Demetrius-Ross/SimMonitor/images/image.png

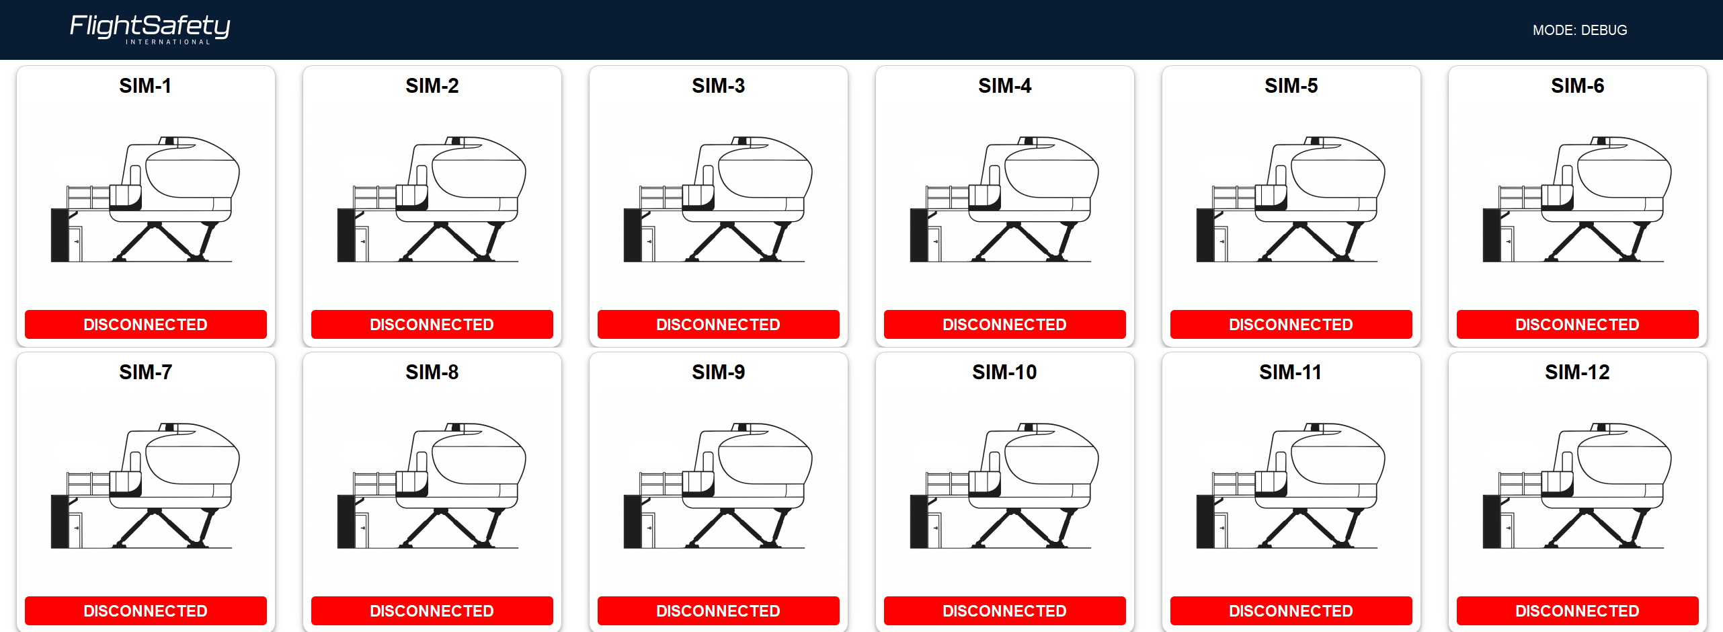
images/image.png
