Demetrius-Ross/SimMonitor/sim_monitor/BACKUP-V1.1/images/FINAL-RAMP-UP.png

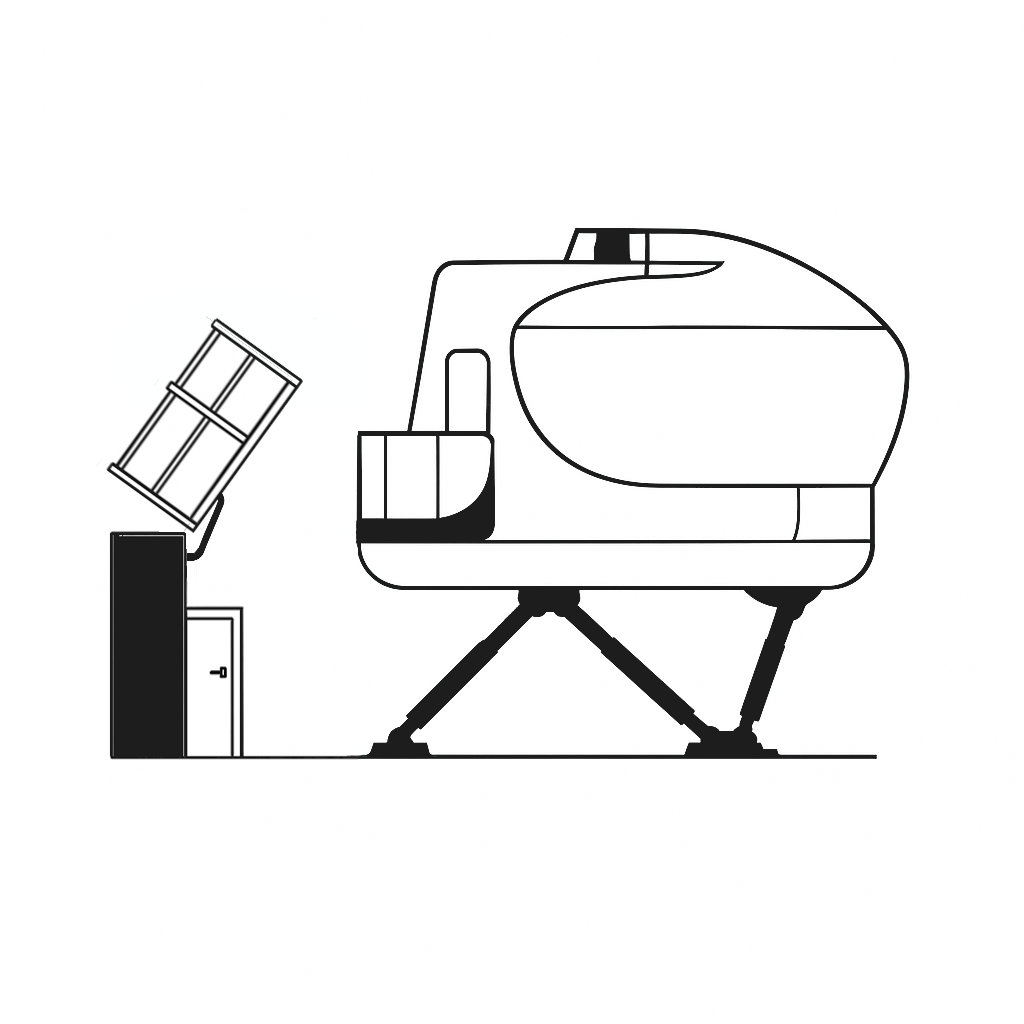
sim_monitor/BACKUP-V1.1/images/FINAL-RAMP-UP.png
