Demetrius-Ross/SimMonitor/sim_monitor/BACKUP-V1.1/images/FINAL-SIM-UP-NO-RAMP.png

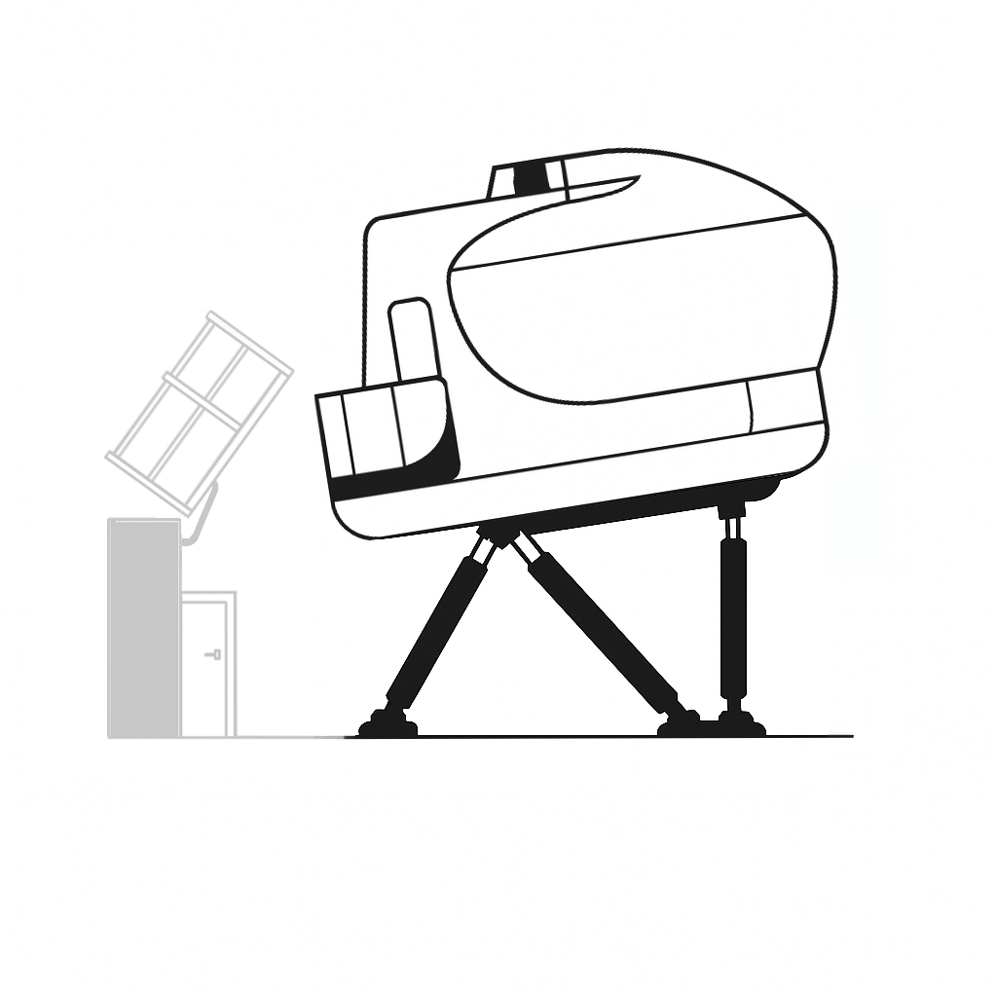
sim_monitor/BACKUP-V1.1/images/FINAL-SIM-UP-NO-RAMP.png
