Demetrius-Ross/SimMonitor/sim_monitor/NEW/images/FINAL-RAMP-UP-ICE.png

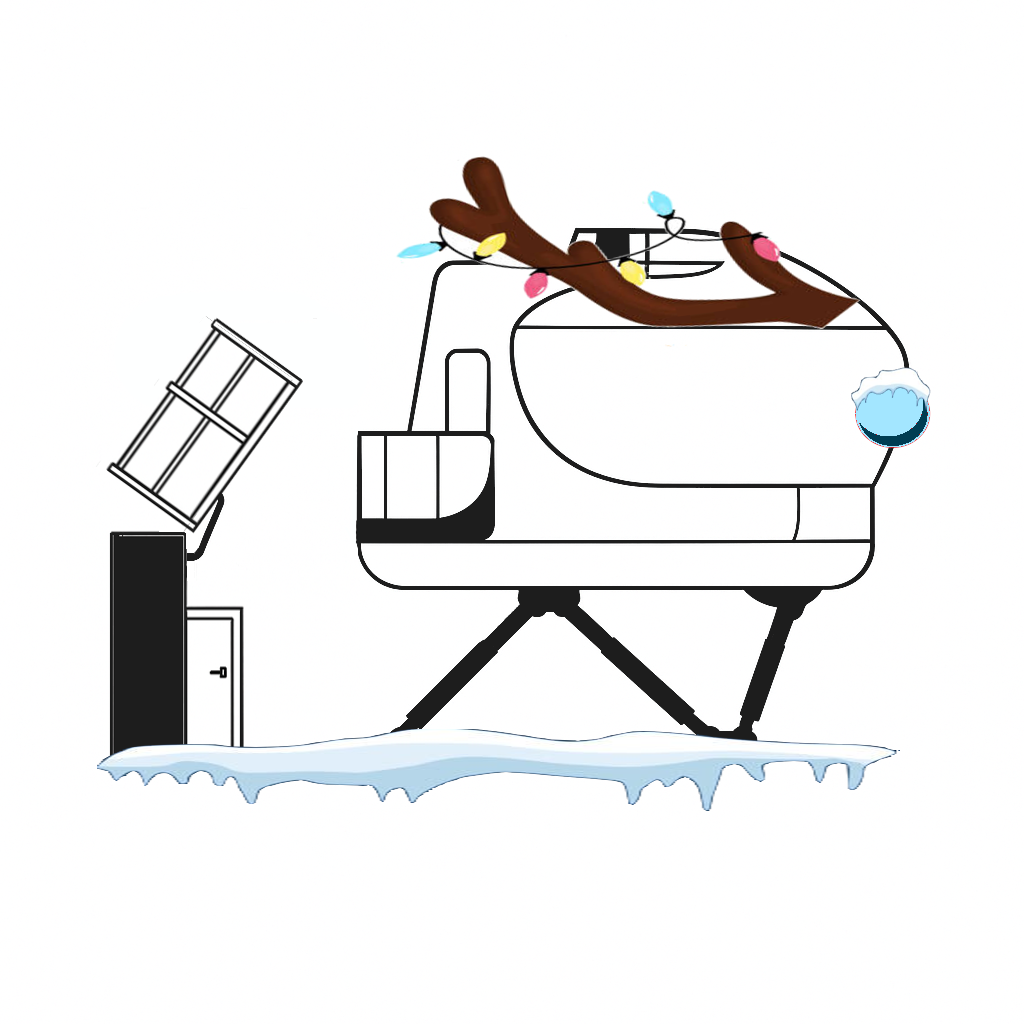
sim_monitor/NEW/images/FINAL-RAMP-UP-ICE.png
