Demetrius-Ross/SimMonitor/sim_monitor/NEW/images/FINAL-SIM-UP-ICE.png

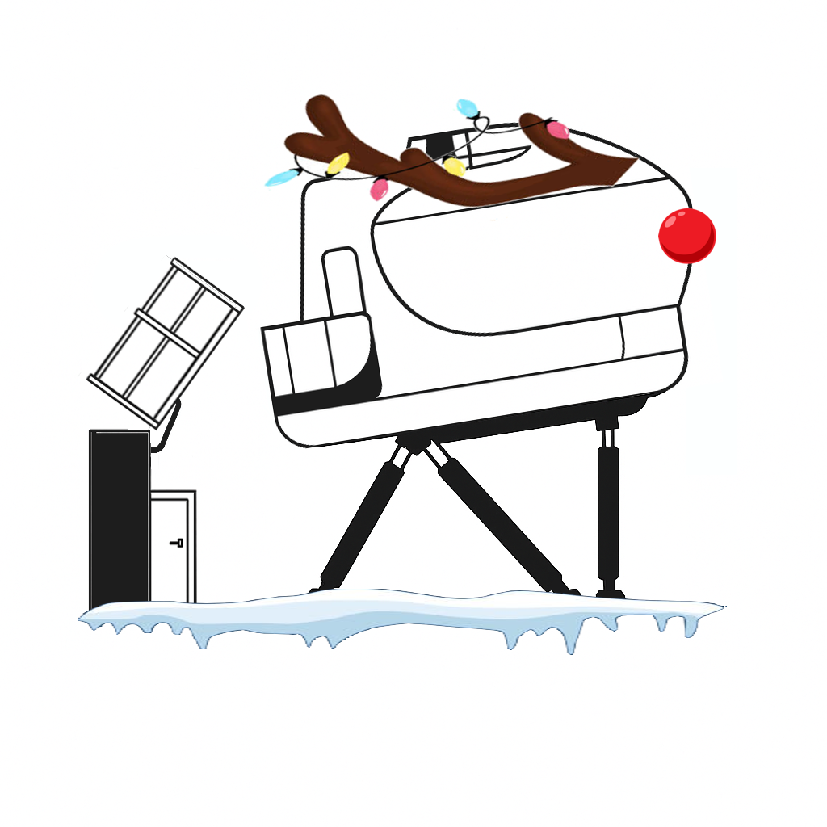
sim_monitor/NEW/images/FINAL-SIM-UP-ICE.png
