Demetrius-Ross/SimMonitor/Hardware-Design/board_MKIV/models/model/COM-16347_SPK.step

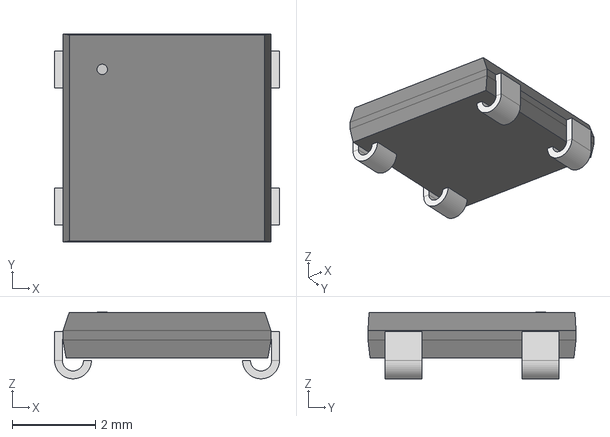
[picture p23: CAD file, 2025-11-21]
Hardware-Design/board_MKIV/models/model/COM-16347_SPK.step
5.41 x 5.00 x 1.60 mm
