Demetrius-Ross/SimMonitor/Hardware-Design/board_telemetry/board_telemetry/models/model/DS01C-254-S-03BE.step

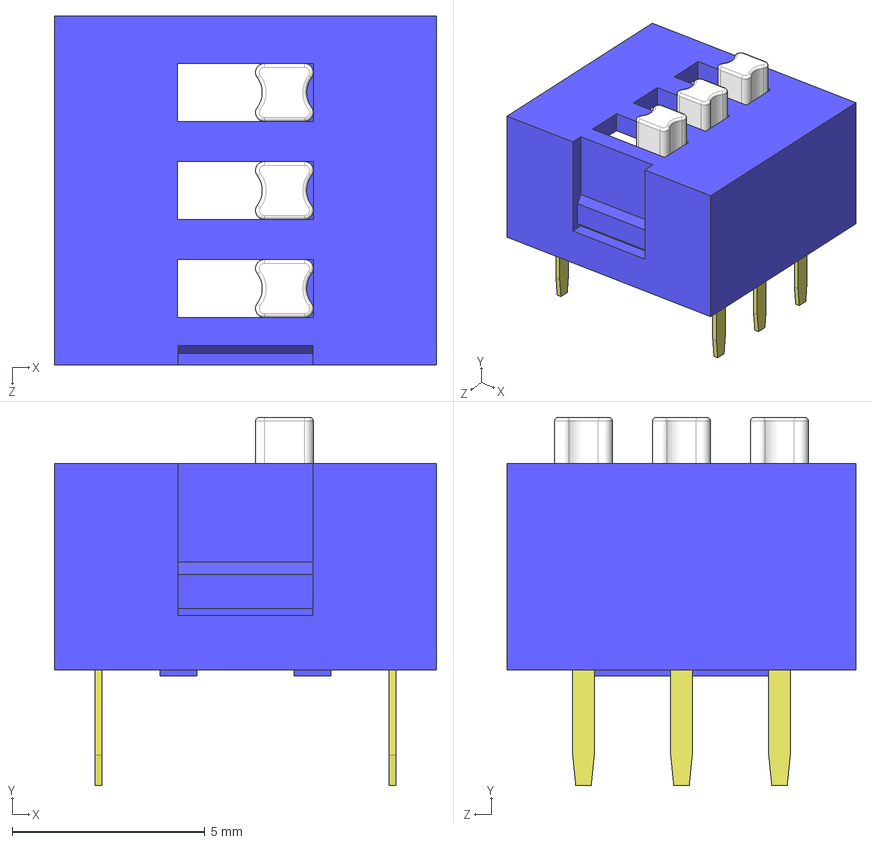
[picture p24: CAD file, 2025-11-19]
Hardware-Design/board_telemetry/board_telemetry/models/model/DS01C-254-S-03BE.step
9.90 x 9.55 x 9.04 mm
