Demetrius-Ross/SimMonitor/Hardware-Design/board_telemetry/board_telemetry/models/model/PB400EEQR1BLK.step

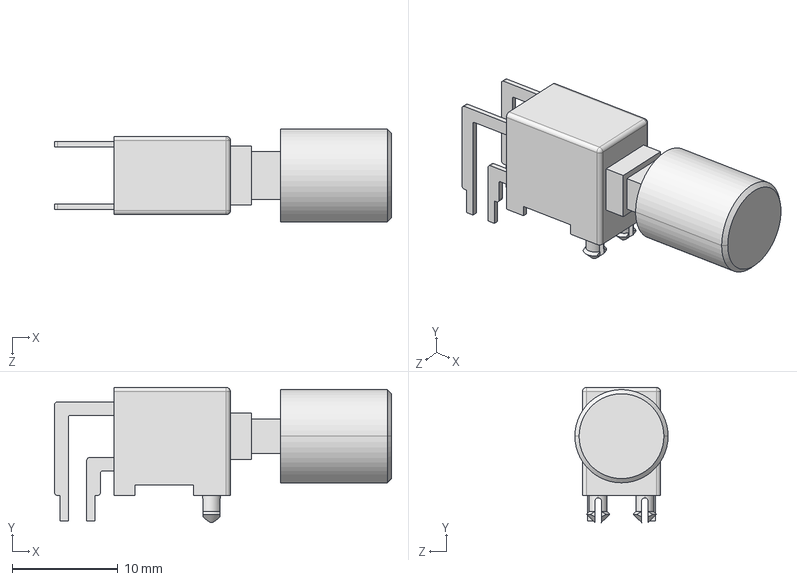
[picture p25: CAD file, 2025-11-15]
Hardware-Design/board_telemetry/board_telemetry/models/model/PB400EEQR1BLK.step
31.8 x 12.7 x 8.80 mm
