Demetrius-Ross/SimMonitor/Hardware-Design/board_telemetry/board_telemetry/models/model/SH-7070TB_7P1X7P3_NDC.step

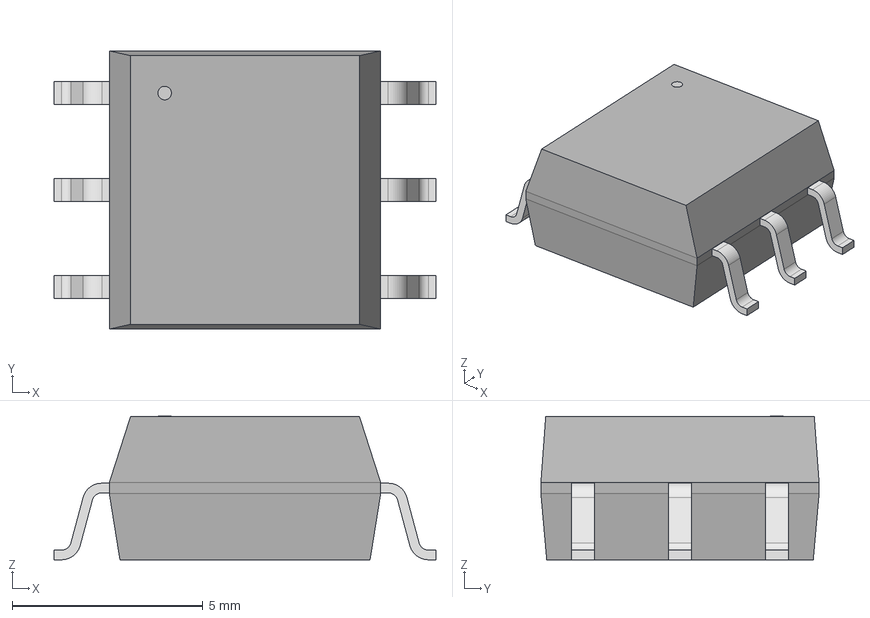
[picture p26: CAD file, 2025-11-15]
Hardware-Design/board_telemetry/board_telemetry/models/model/SH-7070TB_7P1X7P3_NDC.step
10.0 x 7.29 x 3.76 mm
