Demetrius-Ross/SimMonitor/Hardware/board_design/models/model/TO252-3_ROM.step

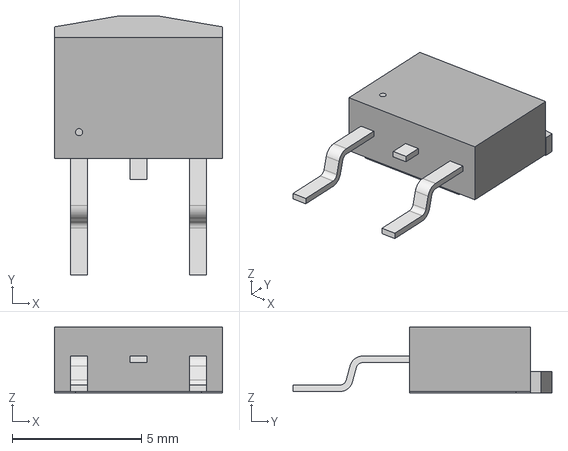
[picture p27: CAD file, 2025-11-06]
Hardware/board_design/models/model/TO252-3_ROM.step
6.50 x 10.0 x 2.54 mm
