Demetrius-Ross/SimMonitor/Hardware-Design/board_telemetry/board_telemetry/models/model/20_pin_straight.STEP

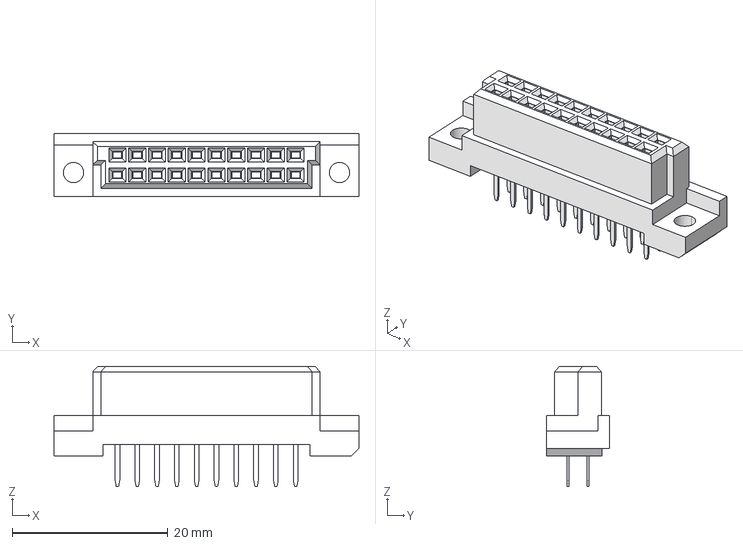
[picture p28: CAD file, 2025-11-13]
Hardware-Design/board_telemetry/board_telemetry/models/model/20_pin_straight.STEP
39.1 x 8.10 x 15.4 mm
