Demetrius-Ross/SimMonitor/Hardware-Design/AllModels/20_pin_90.STEP

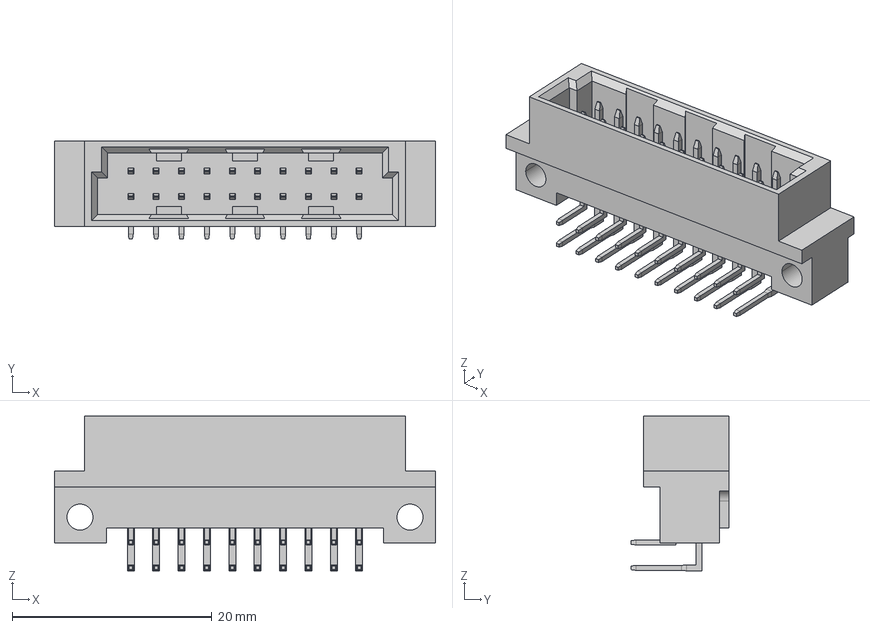
[picture p29: CAD file, 2025-11-13]
Hardware-Design/AllModels/20_pin_90.STEP
38.1 x 9.85 x 15.5 mm
