Demetrius-Ross/SimMonitor/Hardware-Design/board_telemetry/board_telemetry/models/model/D0008A.stp

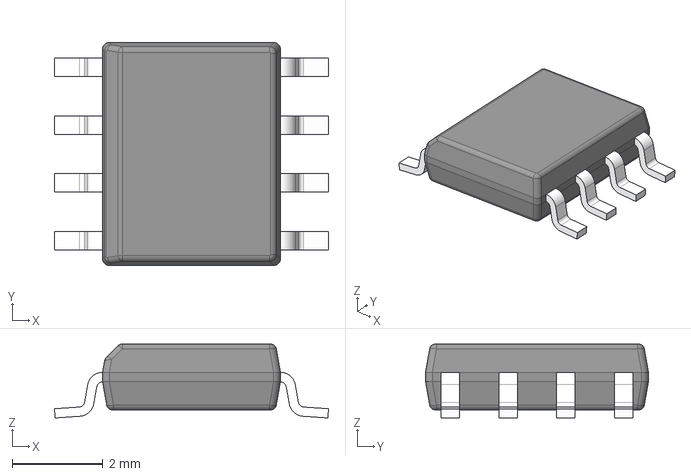
[picture p30: CAD file, 2025-11-06]
Hardware-Design/board_telemetry/board_telemetry/models/model/D0008A.stp
6.02 x 4.90 x 1.63 mm
BODY-SO
LEAD-D0008A x 8
