Demetrius-Ross/SimMonitor/Hardware-Design/AllModels/ERJP08J105V.step

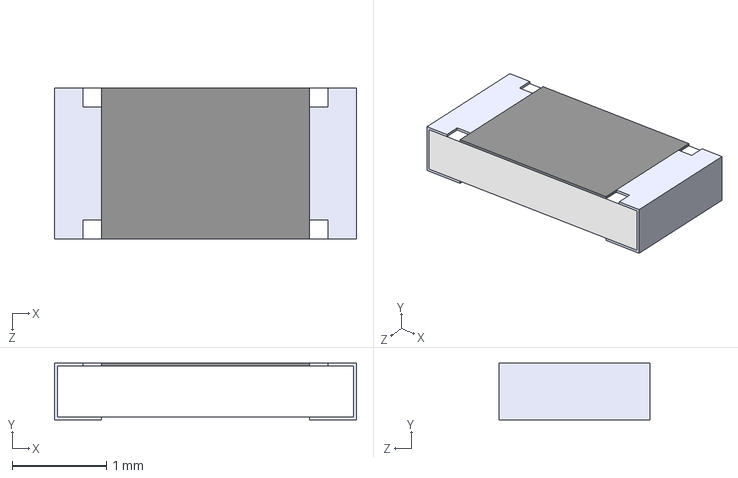
[picture p31: CAD file, 2025-11-06]
Hardware-Design/AllModels/ERJP08J105V.step
3.20 x 0.6 x 1.60 mm
