Demetrius-Ross/SimMonitor/Hardware-Design/board_telemetry/board_telemetry/models/model/BAT46W.step

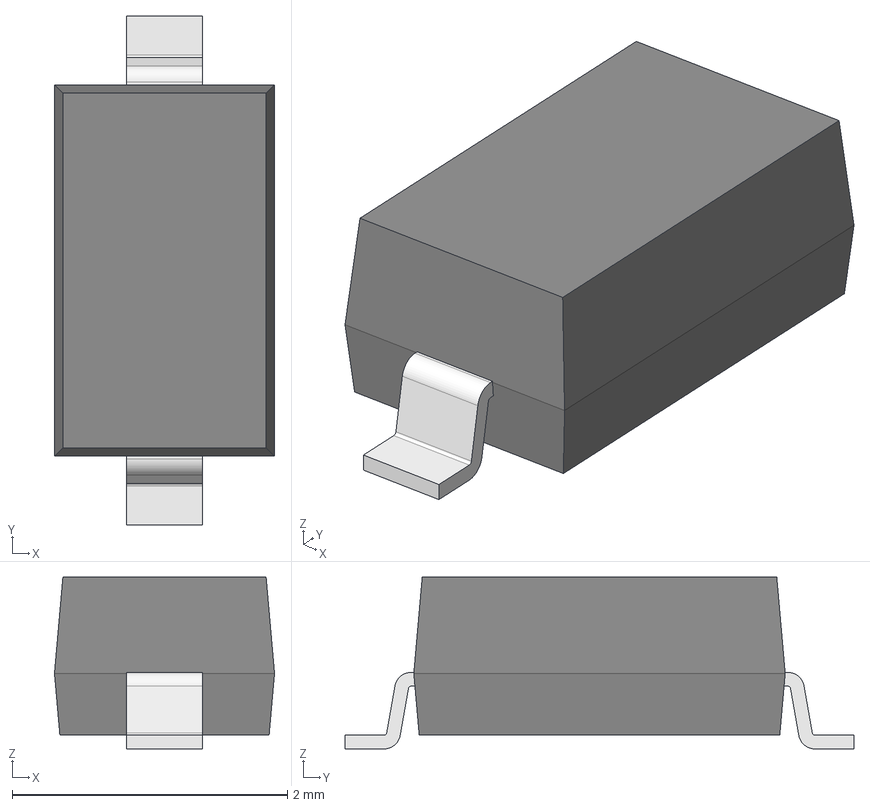
[picture p32: CAD file, 2025-11-06]
Hardware-Design/board_telemetry/board_telemetry/models/model/BAT46W.step
1.60 x 3.70 x 1.25 mm
