Demetrius-Ross/SimMonitor/Hardware-Design/board_telemetry/board_telemetry/models/model/ECA1HM100.step

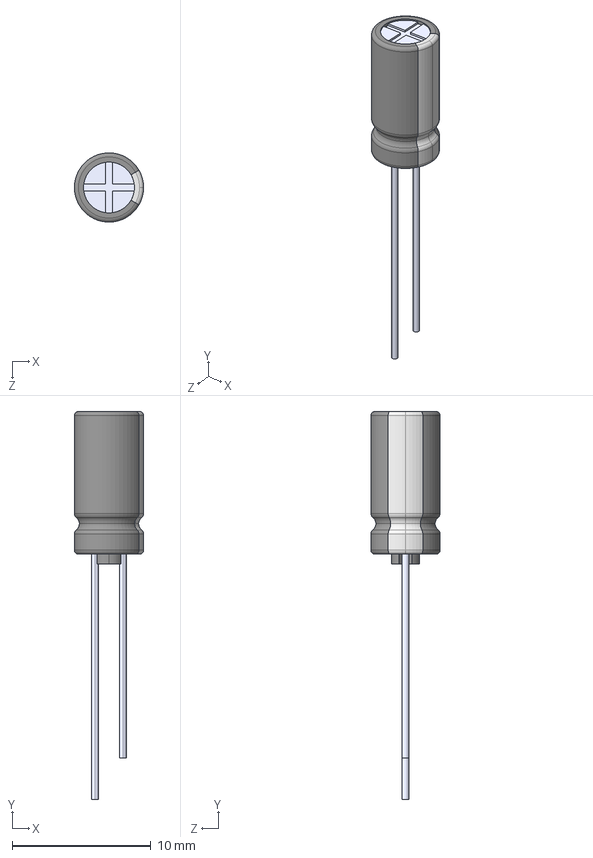
[picture p33: CAD file, 2025-11-06]
Hardware-Design/board_telemetry/board_telemetry/models/model/ECA1HM100.step
5.00 x 28.0 x 4.99 mm
