Demetrius-Ross/SimMonitor/Hardware-Design/AllModels/c-1-2834011-3-2-3d.stp

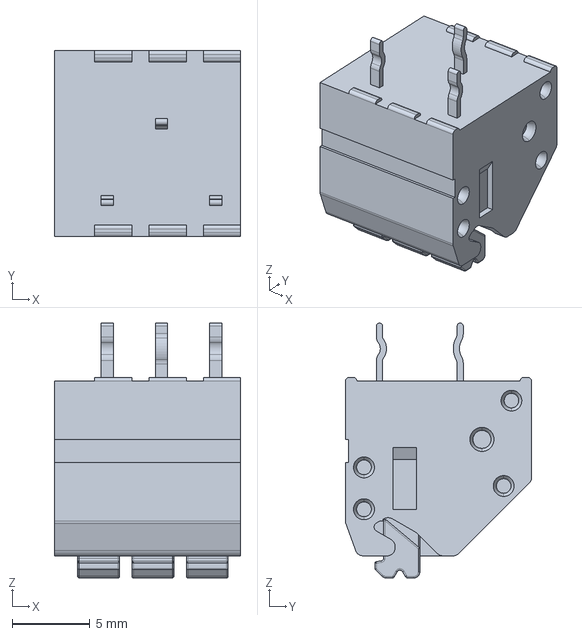
[picture p34: CAD file, 2025-05-02]
Hardware-Design/AllModels/c-1-2834011-3-2-3d.stp
12.0 x 12.0 x 16.4 mm
