Demetrius-Ross/SimMonitor/Hardware-Design/board_telemetry/board_telemetry/models/model/PCAP_10x12_5-THRU-ELECT_NCA.step

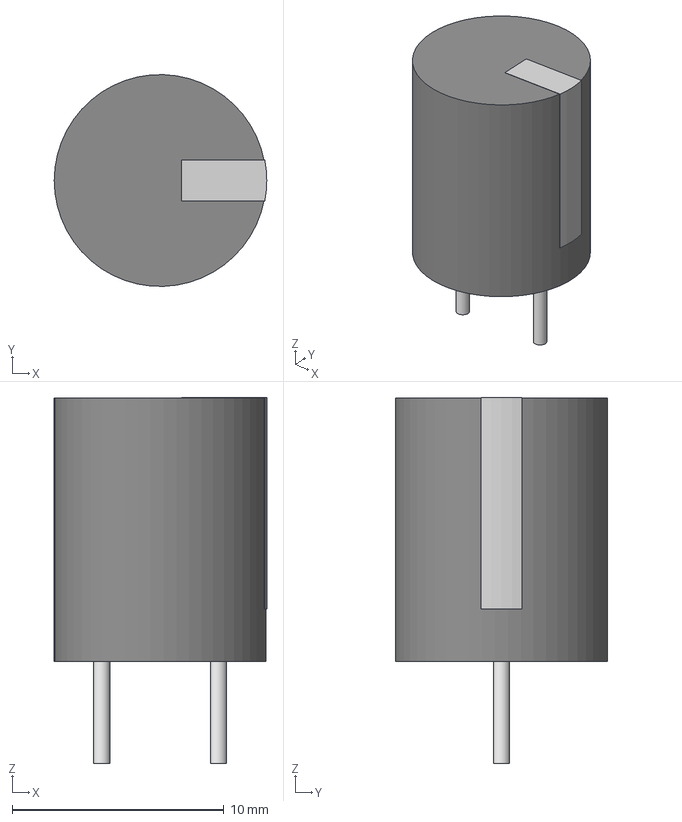
[picture p35: CAD file, 2025-05-02]
Hardware-Design/board_telemetry/board_telemetry/models/model/PCAP_10x12_5-THRU-ELECT_NCA.step
10.0 x 10.0 x 17.3 mm
