Demetrius-Ross/SimMonitor/Hardware-Design/AllModels/TB001-500-09BE.step

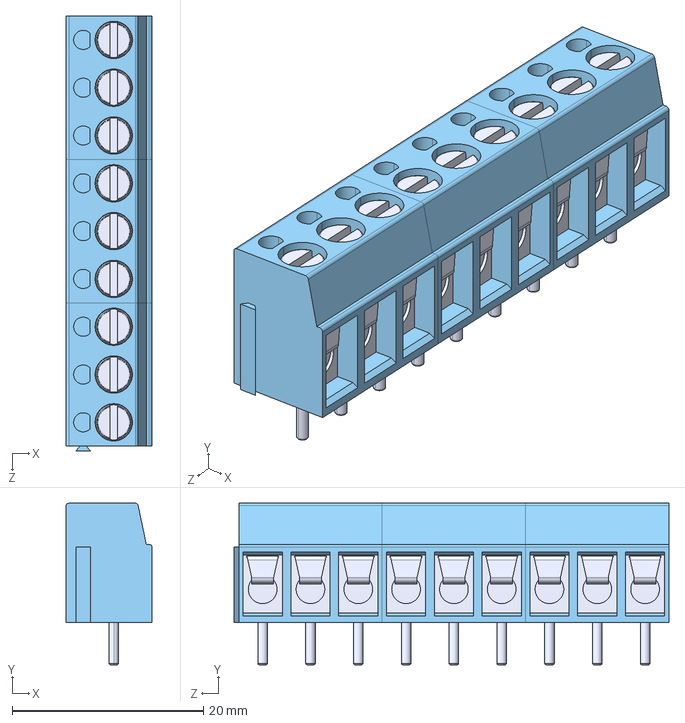
[picture p36: CAD file, 2025-05-02]
Hardware-Design/AllModels/TB001-500-09BE.step
9.00 x 16.9 x 45.5 mm
TB001-500-03P_Blue - S x 3
