Demetrius-Ross/SimMonitor/Hardware-Design/board_telemetry/board_telemetry/models/model/TB001-500-04BE.STEP

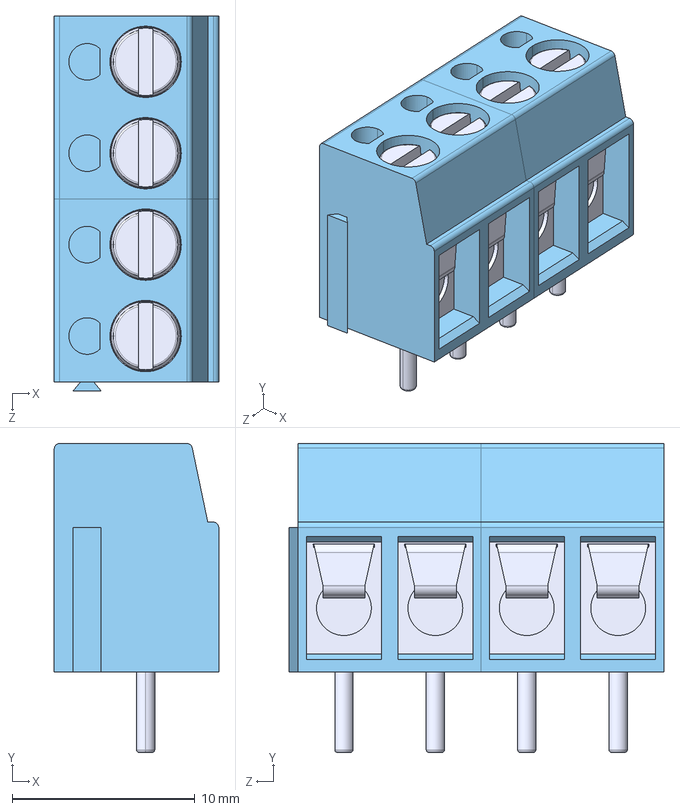
[picture p37: CAD file, 2025-05-02]
Hardware-Design/board_telemetry/board_telemetry/models/model/TB001-500-04BE.STEP
9.00 x 16.9 x 20.5 mm
TB001-500-02P_Blue - S x 2
