Demetrius-Ross/SimMonitor/Hardware-Design/board_telemetry/board_telemetry/models/model/SM04B-SRSS-TB.STEP

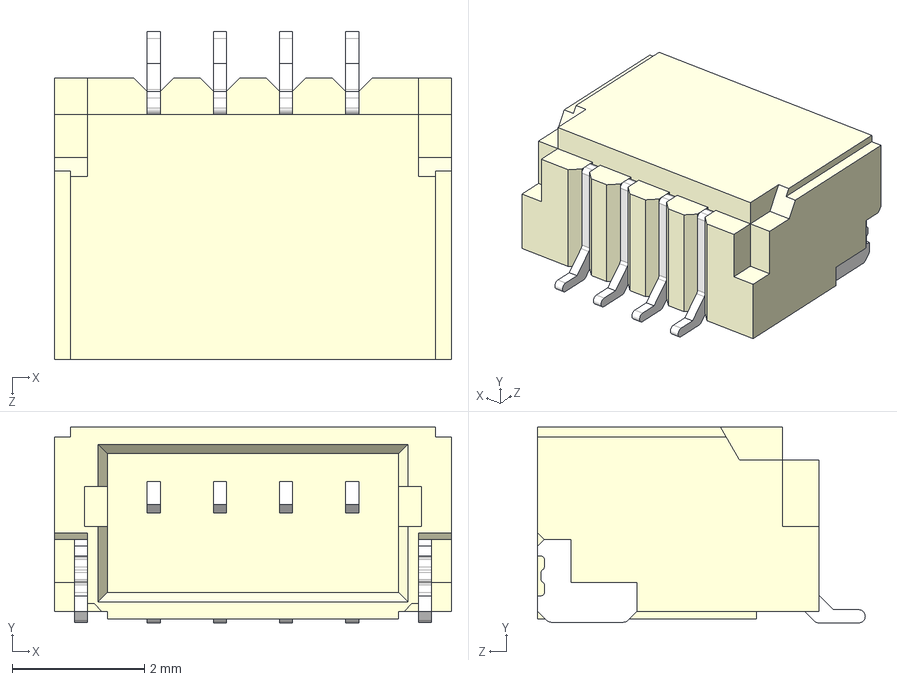
[picture p38: CAD file, 2025-04-26]
Hardware-Design/board_telemetry/board_telemetry/models/model/SM04B-SRSS-TB.STEP
6.00 x 2.96 x 4.95 mm
