Demetrius-Ross/SimMonitor/Hardware-Design/board_telemetry/board_telemetry/models/model/S3B-EH.STEP

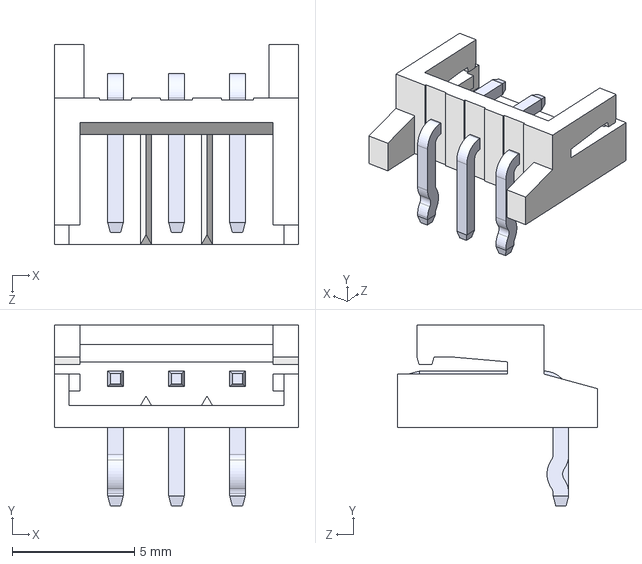
[picture p39: CAD file, 2025-04-26]
Hardware-Design/board_telemetry/board_telemetry/models/model/S3B-EH.STEP
10.0 x 7.40 x 8.20 mm
