Demetrius-Ross/SimMonitor/Hardware-Design/board_telemetry/board_telemetry/models/model/REC5A-2405SW_H2.step

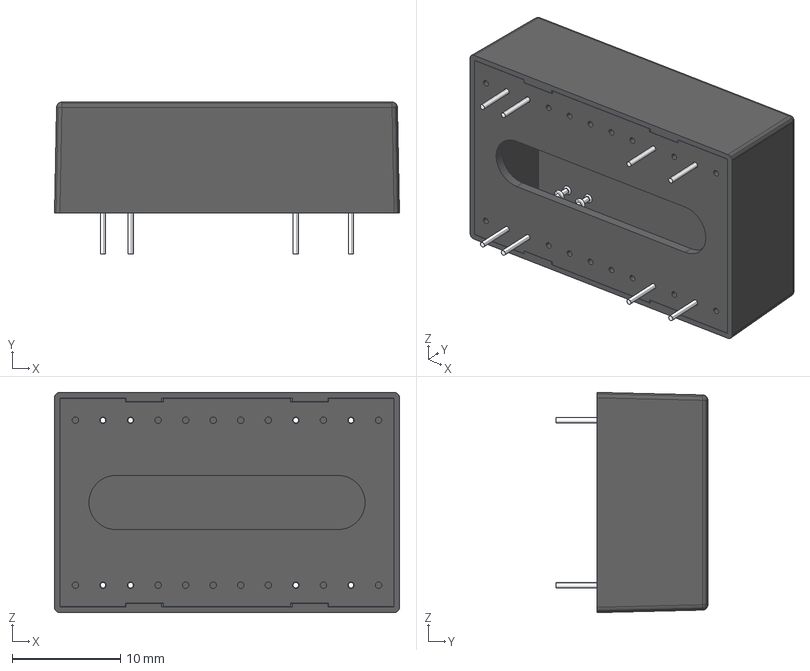
[picture p40: CAD file, 2025-04-04]
Hardware-Design/board_telemetry/board_telemetry/models/model/REC5A-2405SW_H2.step
31.8 x 14.0 x 20.3 mm
