Demetrius-Ross/SimMonitor/Hardware-Design/board_telemetry/board_telemetry/models/model/MP2315GJ-Z.STEP

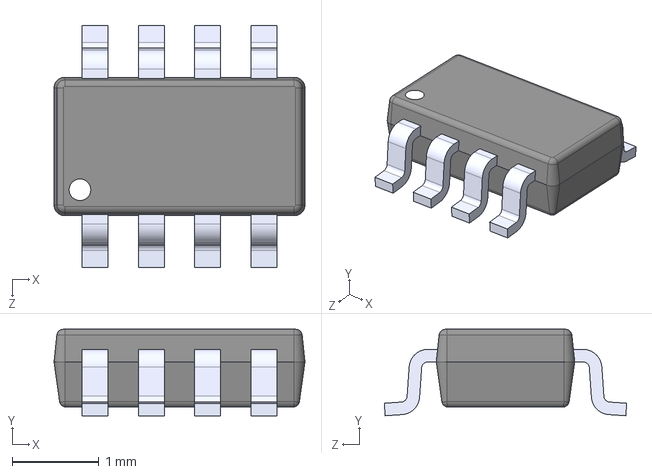
[picture p41: CAD file, 2025-04-04]
Hardware-Design/board_telemetry/board_telemetry/models/model/MP2315GJ-Z.STEP
2.90 x 1.00 x 2.80 mm
