Demetrius-Ross/SimMonitor/Hardware-Design/AllModels/RNCP1206FTD1K10.step

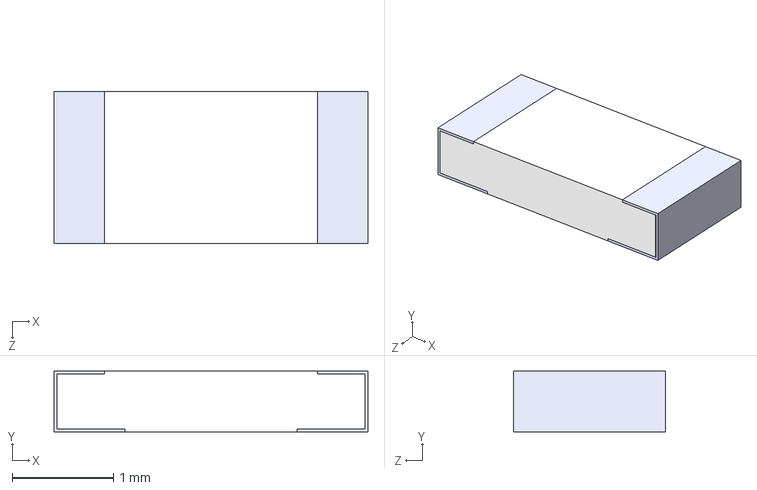
[picture p42: CAD file, 2025-04-04]
Hardware-Design/AllModels/RNCP1206FTD1K10.step
3.10 x 0.6 x 1.50 mm
