Demetrius-Ross/SimMonitor/Hardware-Design/board_telemetry/board_telemetry/models/model/C1206C104K4RACTU.step

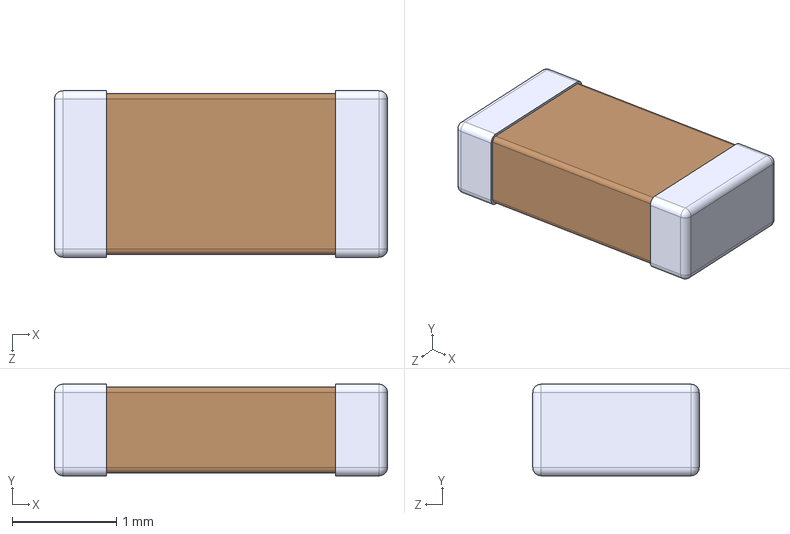
[picture p43: CAD file, 2025-03-08]
Hardware-Design/board_telemetry/board_telemetry/models/model/C1206C104K4RACTU.step
3.20 x 0.88 x 1.60 mm
