Demetrius-Ross/SimMonitor/Hardware-Design/board_telemetry/board_telemetry/models/model/A-DF_09_A_KG-T4S.step

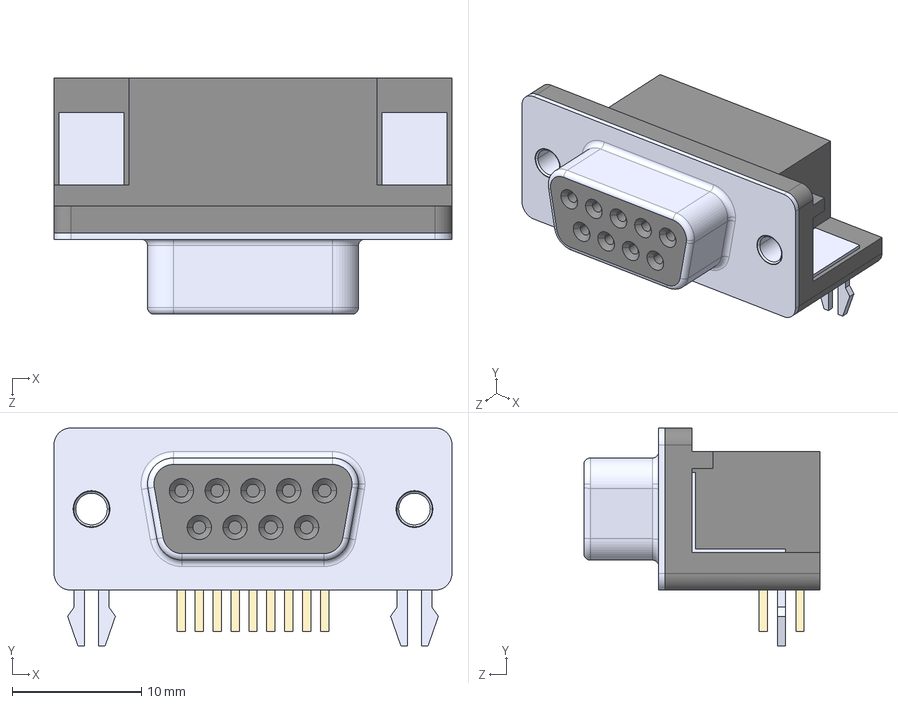
[picture p44: CAD file, 2025-03-08]
Hardware-Design/board_telemetry/board_telemetry/models/model/A-DF_09_A_KG-T4S.step
30.8 x 16.9 x 18.3 mm
