Demetrius-Ross/SimMonitor/Hardware-Design/board_telemetry/board_telemetry/models/model/CRCW120620K0FKEAC.step

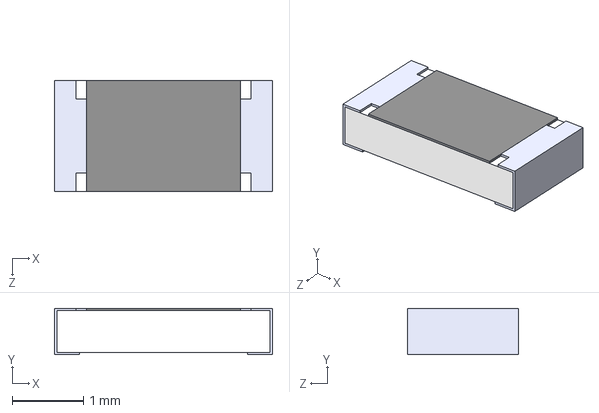
[picture p45: CAD file, 2025-03-08]
Hardware-Design/board_telemetry/board_telemetry/models/model/CRCW120620K0FKEAC.step
3.05 x 0.65 x 1.55 mm
